pbmelo/aerogel-machine-monitoring/screenshots/aerogel_shield_front_w_components.png

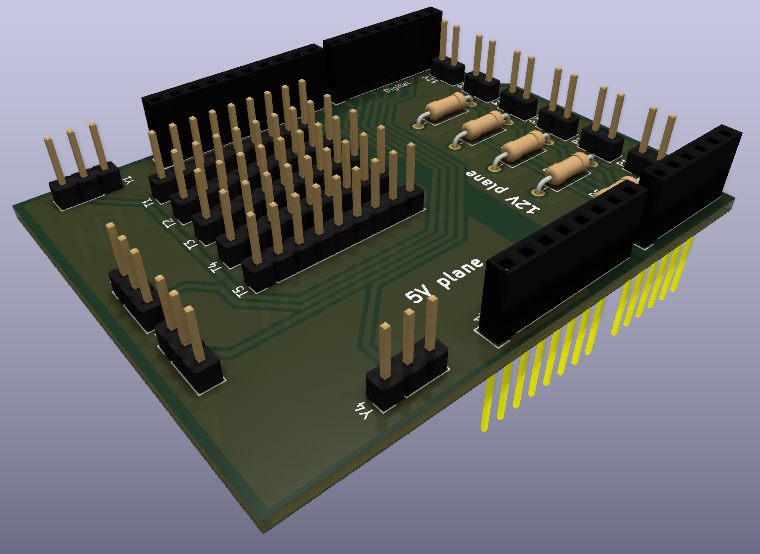
screenshots/aerogel_shield_front_w_components.png
