pbmelo/aerogel-machine-monitoring/screenshots/physical-pcb-soldered.png

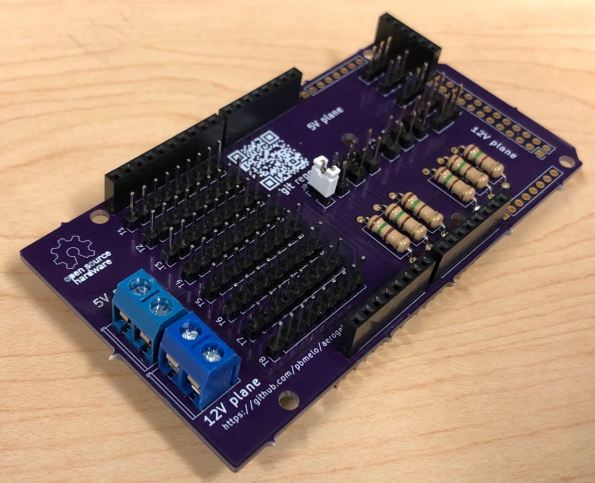
screenshots/physical-pcb-soldered.png
